mawildoer/delta_bot/hardware/flat_patterns/spine_stiffening x2.dxf

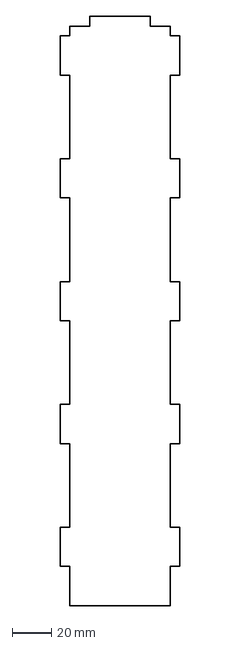
[picture p18: CAD file, 2018-10-24]
hardware/flat_patterns/spine_stiffening x2.dxf
60.9 x 300.0 mm
