mawildoer/delta_bot/hardware/flat_patterns/mount_side x2.dxf

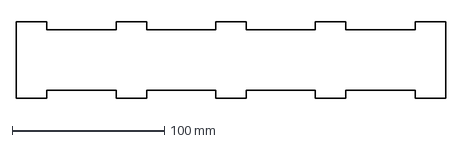
[picture p19: CAD file, 2018-10-24]
hardware/flat_patterns/mount_side x2.dxf
282.0 x 50.0 mm
