mawildoer/delta_bot/hardware/flat_patterns/spine_left x1.dxf

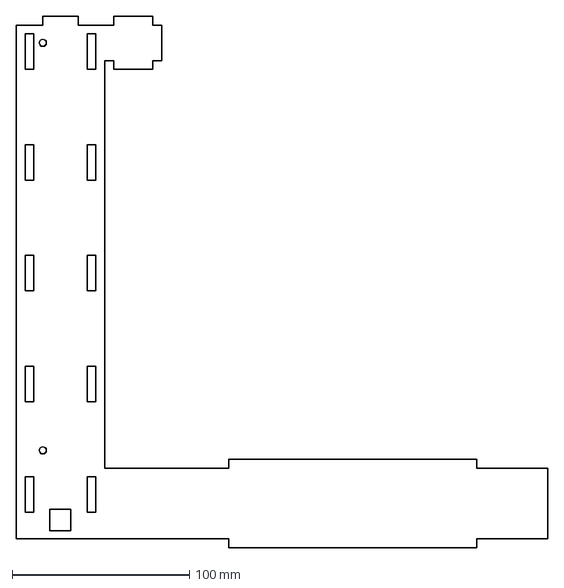
[picture p20: CAD file, 2018-10-24]
hardware/flat_patterns/spine_left x1.dxf
300.0 x 300.0 mm
