mawildoer/delta_bot/hardware/flat_patterns/mount_top x1.dxf

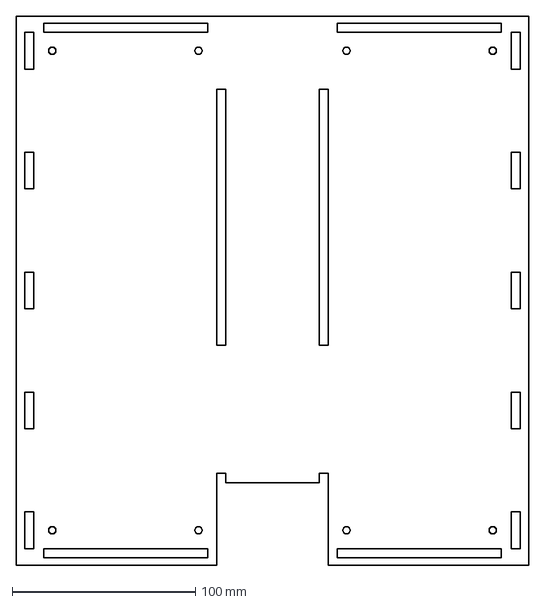
[picture p21: CAD file, 2018-10-24]
hardware/flat_patterns/mount_top x1.dxf
280.0 x 300.0 mm
