mawildoer/delta_bot/hardware/flat_patterns/mount_bottom x1.dxf

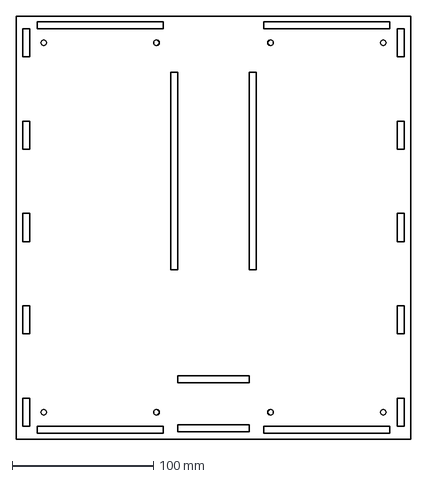
[picture p22: CAD file, 2018-10-24]
hardware/flat_patterns/mount_bottom x1.dxf
280.0 x 300.0 mm
